demute/smart_lights/firmware/TurtleBoard/MBED_USBDeviceHT/targets/TARGET_STM/xUSBHAL_IP_DEVICE.h

/* Copyright (c) 2017 mbed.org, MIT License
*
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
* THE SOFTWARE IS PROVIDED "AS IS", WITHOUT WARRANTY OF ANY KIND, EXPRESS OR IMPLIED, INCLUDING
* BUT NOT LIMITED TO THE WARRANTIES OF MERCHANTABILITY, FITNESS FOR A PARTICULAR PURPOSE AND
* NONINFRINGEMENT. IN NO EVENT SHALL THE AUTHORS OR COPYRIGHT HOLDERS BE LIABLE FOR ANY CLAIM,
* DAMAGES OR OTHER LIABILITY, WHETHER IN AN ACTION OF CONTRACT, TORT OR OTHERWISE, ARISING FROM,
* OUT OF OR IN CONNECTION WITH THE SOFTWARE OR THE USE OR OTHER DEALINGS IN THE SOFTWARE.
*/
#ifndef XUSBHAL_IP_DEVICE_H
#define XUSBHAL_IP_DEVICE_H

#if defined(TARGET_NUCLEO_F303ZE)
#define USBHAL_IRQn  USB_LP_CAN_RX0_IRQn

#elif defined(TARGET_NUCLEO_F103RB)
#define USBHAL_IRQn  USB_LP_CAN1_RX0_IRQn

#elif defined(TARGET_DISCO_L072CZ_LRWAN1) || \
      defined(TARGET_DISCO_L053C8) || \
	  defined(TARGET_STM32L4)
#define USBHAL_IRQn  USB_IRQn

#else
#error "USB IRQ is not configured !"
#endif

#if defined(TARGET_STM32L4) || defined(TARGET_DISCO_L072CZ_LRWAN1)
extern "C" { void pin_function(PinName pin, int function); }
#endif


#define NB_ENDPOINT  8 // Must be a multiple of 4 bytes

#define MAXTRANSFER_SIZE  0x200

#define FIFO_USB_RAM_SIZE (MAXTRANSFER_SIZE + MAX_PACKET_SIZE_EP0 + MAX_PACKET_SIZE_EP1 + MAX_PACKET_SIZE_EP2 + MAX_PACKET_SIZE_EP3)

#if (FIFO_USB_RAM_SIZE > 0x500)
#error "FIFO dimensioning incorrect"
#endif

typedef struct
{
    xUSBHAL *inst;

    void (xUSBHAL::*bus_reset)(void);
    void (xUSBHAL::*sof)(int frame);
    void (xUSBHAL::*connect_change)(unsigned int connected);
    void (xUSBHAL::*suspend_change)(unsigned int suspended);
    void (xUSBHAL::*ep0_setup)(void);
    void (xUSBHAL::*ep0_in)(void);
    void (xUSBHAL::*ep0_out)(void);
    void (xUSBHAL::*ep0_read)(void);
    bool (xUSBHAL::*ep_realise)(uint8_t endpoint, uint32_t maxPacket, uint32_t flags);
    bool (xUSBHAL::*epCallback[(2 * NB_ENDPOINT) - 2])(void);

    uint8_t epComplete[2 * NB_ENDPOINT];

    /* Memorize dummy buffer used for reception */
    uint32_t pBufRx[MAXTRANSFER_SIZE >> 2];
    uint32_t pBufRx0[MAX_PACKET_SIZE_EP0 >> 2];

    gpio_t usb_switch;
} xUSBHAL_Private_t;

uint32_t HAL_PCDEx_GetTxFiFo(PCD_HandleTypeDef *hpcd, uint8_t fifo)
{
    return 1024;
}

void HAL_PCD_SOFCallback(PCD_HandleTypeDef *hpcd) 
{
    xUSBHAL_Private_t *priv=((xUSBHAL_Private_t *)(hpcd->pData));
    xUSBHAL *obj= priv->inst;
    uint32_t sofnum = (hpcd->Instance->FNR) & USB_FNR_FN;
    void (xUSBHAL::*func)(int frame) = priv->sof;
    (obj->*func)(sofnum);
}

void HAL_PCDEx_SetConnectionState(PCD_HandleTypeDef *hpcd, uint8_t state)
{
    xUSBHAL_Private_t *priv = ((xUSBHAL_Private_t *)(hpcd->pData));
#if defined(TARGET_NUCLEO_F103RB)
    gpio_write(&(priv->usb_switch), !state);
#else
    gpio_write(&(priv->usb_switch), state);
#endif
}

xUSBHAL *xUSBHAL::instance;

xUSBHAL::xUSBHAL(void) {
    xUSBHAL_Private_t *HALPriv = new(xUSBHAL_Private_t);

    hpcd.Instance = USB;

    memset(&hpcd.Init, 0, sizeof(hpcd.Init));
    hpcd.Init.dev_endpoints = NB_ENDPOINT;
    hpcd.Init.ep0_mps = MAX_PACKET_SIZE_EP0;
    hpcd.Init.phy_itface = PCD_PHY_EMBEDDED;
    hpcd.Init.Sof_enable = 1;
    hpcd.Init.speed = PCD_SPEED_FULL;

    // Pass instance for usage inside call back
    HALPriv->inst = this;
    HALPriv->bus_reset = &xUSBHAL::busReset;
    HALPriv->suspend_change = &xUSBHAL::suspendStateChanged;
    HALPriv->connect_change = &xUSBHAL::connectStateChanged;
    HALPriv->sof = &xUSBHAL::SOF;
    HALPriv->ep0_setup = &xUSBHAL::EP0setupCallback;
    HALPriv->ep_realise = &xUSBHAL::realiseEndpoint;
    HALPriv->ep0_in = &xUSBHAL::EP0in;
    HALPriv->ep0_out = &xUSBHAL::EP0out;
    HALPriv->ep0_read = &xUSBHAL::EP0read;
    HALPriv->epCallback[0] = &xUSBHAL::EP1_OUT_callback;
    HALPriv->epCallback[1] = &xUSBHAL::EP1_IN_callback;
    HALPriv->epCallback[2] = &xUSBHAL::EP2_OUT_callback;
    HALPriv->epCallback[3] = &xUSBHAL::EP2_IN_callback;
    HALPriv->epCallback[4] = &xUSBHAL::EP3_OUT_callback;
    HALPriv->epCallback[5] = &xUSBHAL::EP3_IN_callback;
    instance = this;

    // Configure USB pins and other clocks
#if defined(TARGET_NUCLEO_F303ZE)
    __HAL_RCC_GPIOA_CLK_ENABLE();
    pin_function(PA_11, STM_PIN_DATA(STM_MODE_AF_PP, GPIO_NOPULL, GPIO_AF14_USB)); // DM
    pin_function(PA_12, STM_PIN_DATA(STM_MODE_AF_PP, GPIO_NOPULL, GPIO_AF14_USB)); // DP
    __HAL_RCC_GPIOG_CLK_ENABLE();
    gpio_init_out(&HALPriv->usb_switch, PG_6);

#elif defined(TARGET_NUCLEO_F103RB)
    // Make sure to connect a 1.5K resistor between USB-DP PA12 pin and +3.3V
    __HAL_RCC_GPIOA_CLK_ENABLE();
    pin_function(PA_11, STM_PIN_DATA(STM_MODE_AF_PP, GPIO_PULLUP, GPIO_MODE_AF_INPUT)); // DM
    pin_function(PA_12, STM_PIN_DATA(STM_MODE_AF_PP, GPIO_PULLUP, GPIO_MODE_AF_INPUT)); // DP

#elif defined(TARGET_DISCO_L072CZ_LRWAN1) || \
      defined(TARGET_DISCO_L053C8)
    __HAL_RCC_GPIOA_CLK_ENABLE();
    pin_function(PA_11, STM_PIN_DATA(STM_MODE_AF_PP, GPIO_NOPULL, GPIO_AF2_USB)); // DM
    pin_function(PA_12, STM_PIN_DATA(STM_MODE_AF_PP, GPIO_NOPULL, GPIO_AF2_USB)); // DP
    
#elif defined(TARGET_STM32L4)
    __HAL_RCC_GPIOA_CLK_ENABLE();
	pin_function(PA_11, STM_PIN_DATA(STM_MODE_AF_PP, GPIO_NOPULL, GPIO_AF10_USB_FS)); // DM
	pin_function(PA_12, STM_PIN_DATA(STM_MODE_AF_PP, GPIO_NOPULL, GPIO_AF10_USB_FS)); // DP
    __HAL_RCC_PWR_CLK_ENABLE();
    HAL_PWREx_EnableVddUSB();

#else
#error "USB pins are not configured !"
#endif

    __HAL_RCC_USB_CLK_ENABLE();
    __HAL_RCC_SYSCFG_CLK_ENABLE();

    // Configure PCD and FIFOs
    hpcd.pData = (void*)HALPriv;
    hpcd.State = HAL_PCD_STATE_RESET;
    HAL_PCD_Init(&hpcd);

    // EP0
    HAL_PCDEx_PMAConfig(&hpcd, 0x00, PCD_SNG_BUF, 0x30);
    HAL_PCDEx_PMAConfig(&hpcd, 0x80, PCD_SNG_BUF, 0x70);
    // EP1
    HAL_PCDEx_PMAConfig(&hpcd, 0x01, PCD_SNG_BUF, 0x90);
    HAL_PCDEx_PMAConfig(&hpcd, 0x81, PCD_SNG_BUF, 0xb0);
    // EP2
    HAL_PCDEx_PMAConfig(&hpcd, 0x02, PCD_SNG_BUF, 0x100);
    HAL_PCDEx_PMAConfig(&hpcd, 0x82, PCD_SNG_BUF, 0x120);
    // EP3
    HAL_PCDEx_PMAConfig(&hpcd, 0x03, PCD_DBL_BUF, 0x018000b0);
    HAL_PCDEx_PMAConfig(&hpcd, 0x83, PCD_SNG_BUF, 0xb0);

    // Configure interrupt vector
    NVIC_SetVector(USBHAL_IRQn, (uint32_t)&_usbisr);
    NVIC_SetPriority(USBHAL_IRQn, 1);

    HAL_PCD_Start(&hpcd);
}

#endif // xUSBHAL_IP_DEVICE_H
